estherbm/Open-BioBand/Images/3D/1.png

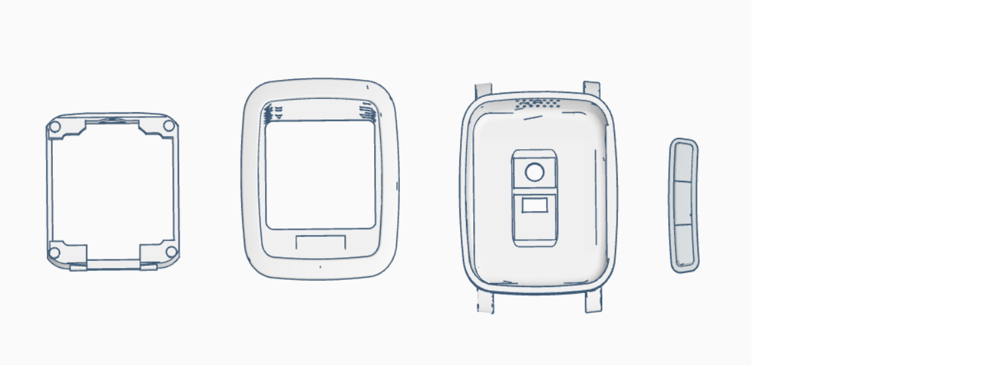
Images/3D/1.png
