estherbm/Open-BioBand/Images/3D/2.png

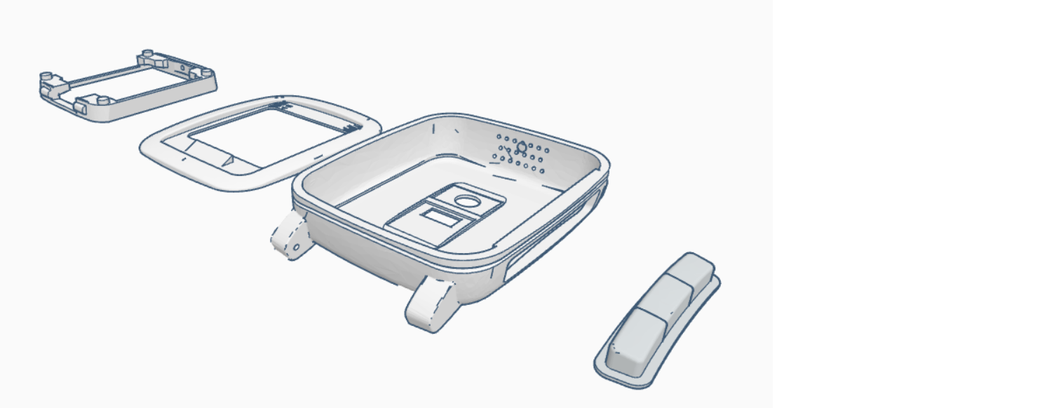
Images/3D/2.png
