estherbm/Open-BioBand/Images/3D/3.png

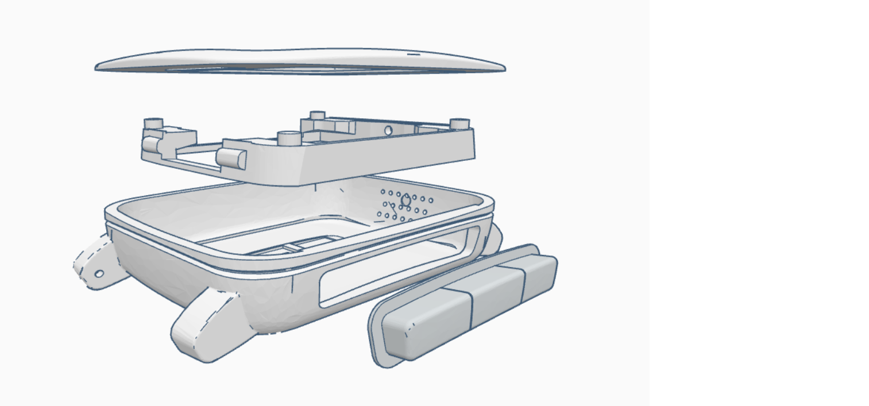
Images/3D/3.png
