estherbm/Open-BioBand/Images/3D/4.png

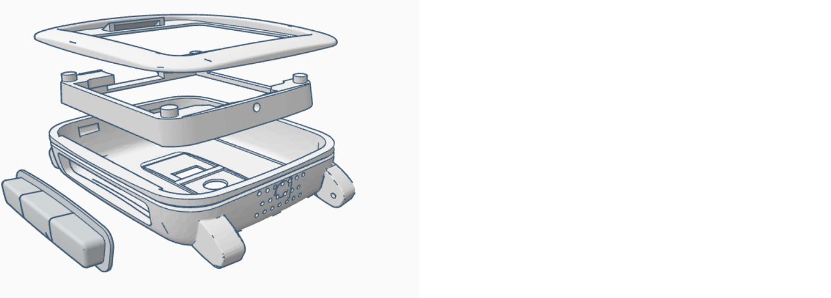
Images/3D/4.png
