estherbm/Open-BioBand/Images/3D/5.png

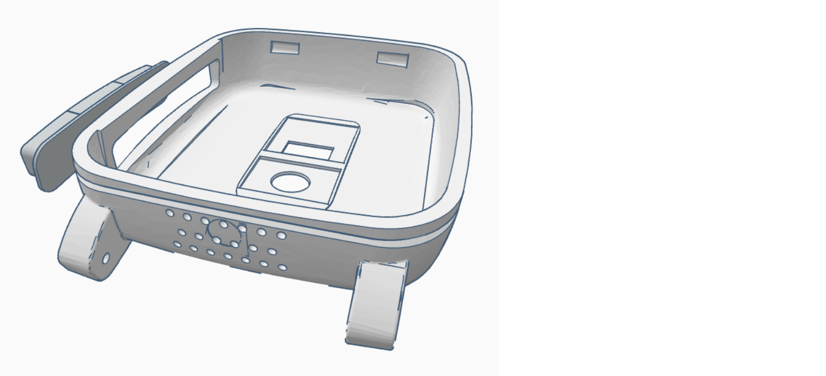
Images/3D/5.png
