estherbm/Open-BioBand/Images/3D/6.png

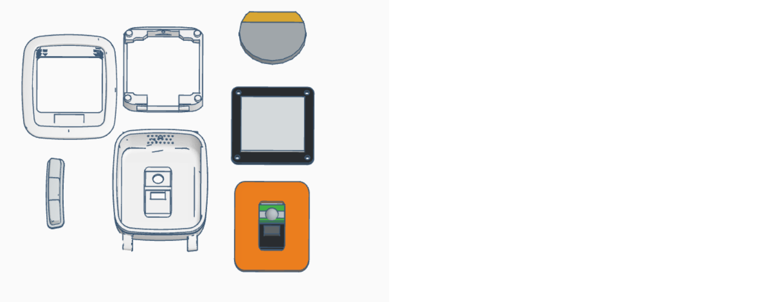
Images/3D/6.png
