estherbm/Open-BioBand/Images/3D/8.png

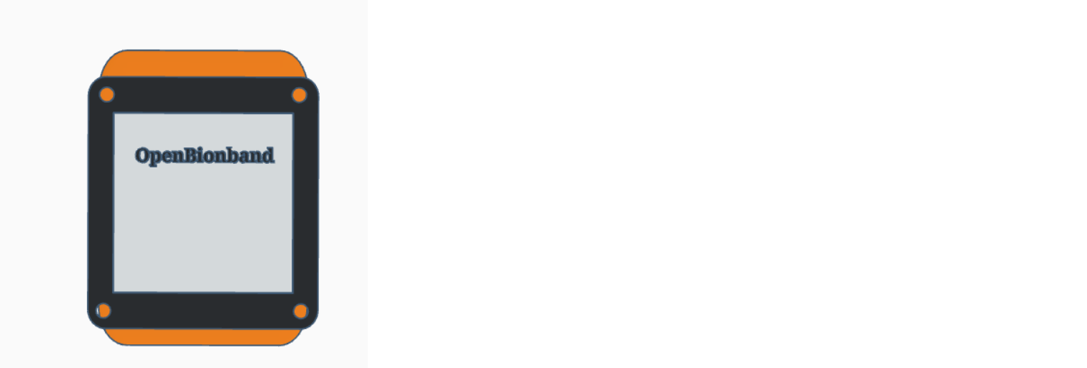
Images/3D/8.png
