estherbm/Open-BioBand/Images/3D/9.png

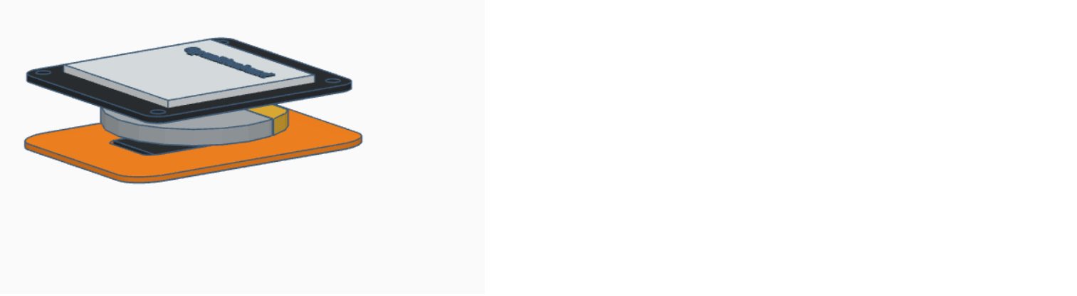
Images/3D/9.png
