estherbm/Open-BioBand/Images/3D/10.png

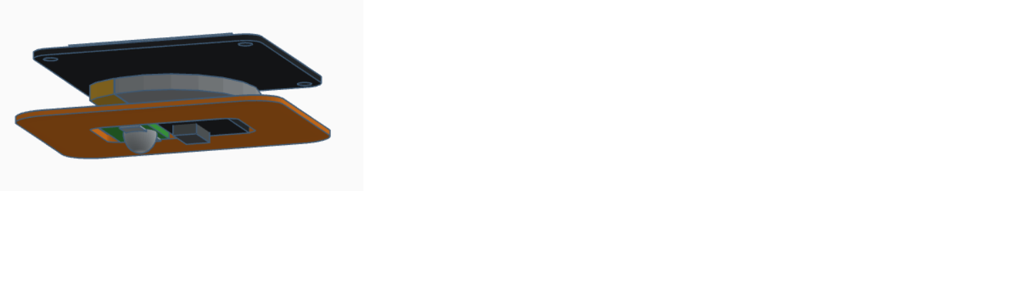
Images/3D/10.png
