estherbm/Open-BioBand/Images/3D/11.png

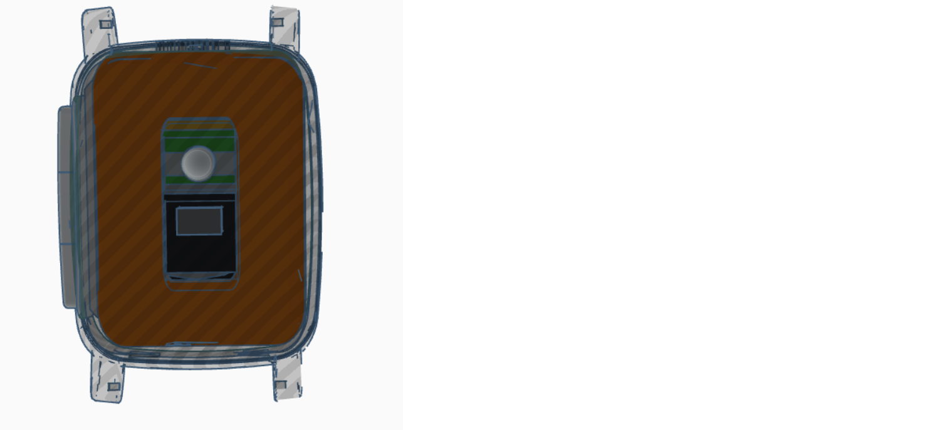
Images/3D/11.png
