estherbm/Open-BioBand/Images/3D/12.png

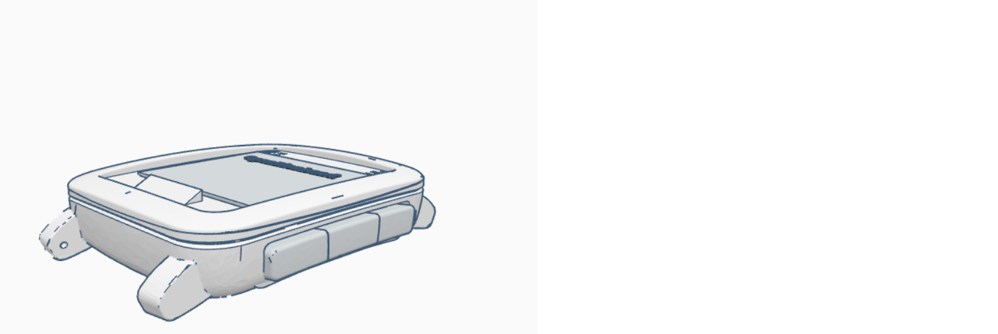
Images/3D/12.png
