estherbm/Open-BioBand/Images/3D/13.png

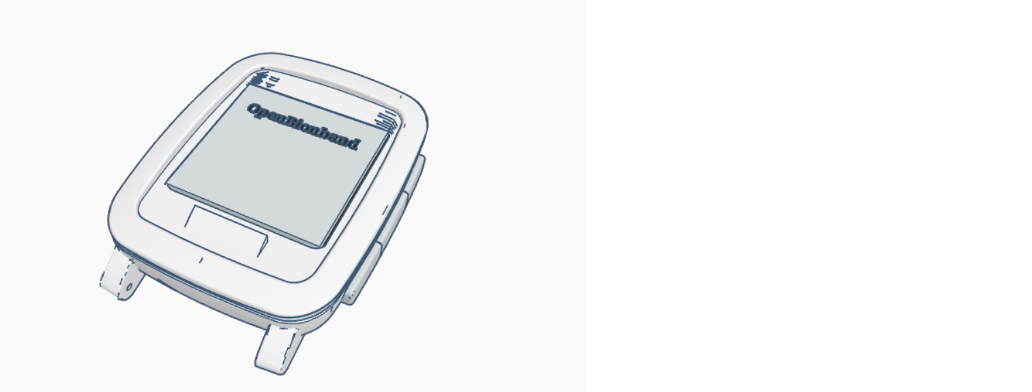
Images/3D/13.png
