estherbm/Open-BioBand/Images/3D/14.png

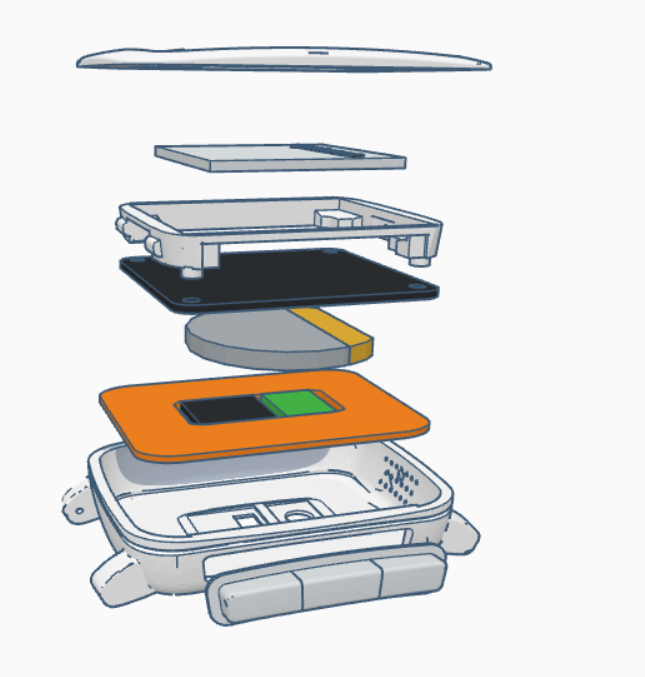
Images/3D/14.png
