estherbm/Open-BioBand/Images/3D/15.png

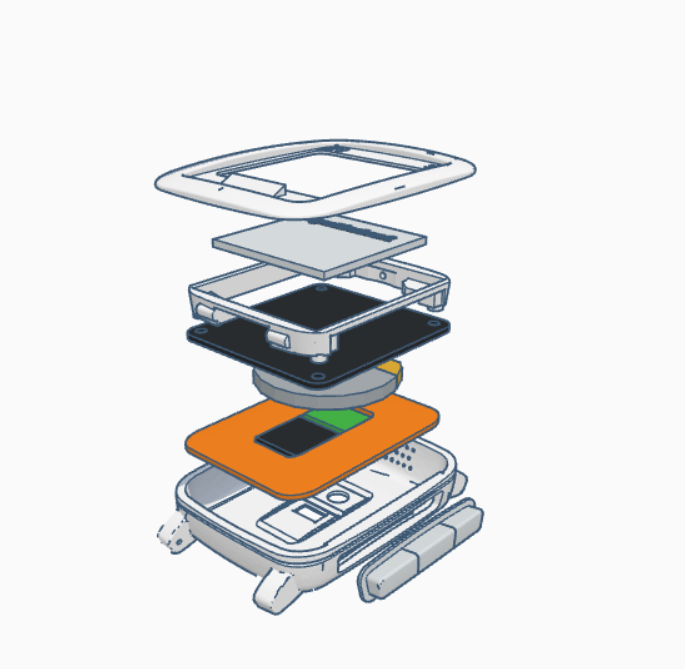
Images/3D/15.png
