estherbm/Open-BioBand/Images/3D/16.png

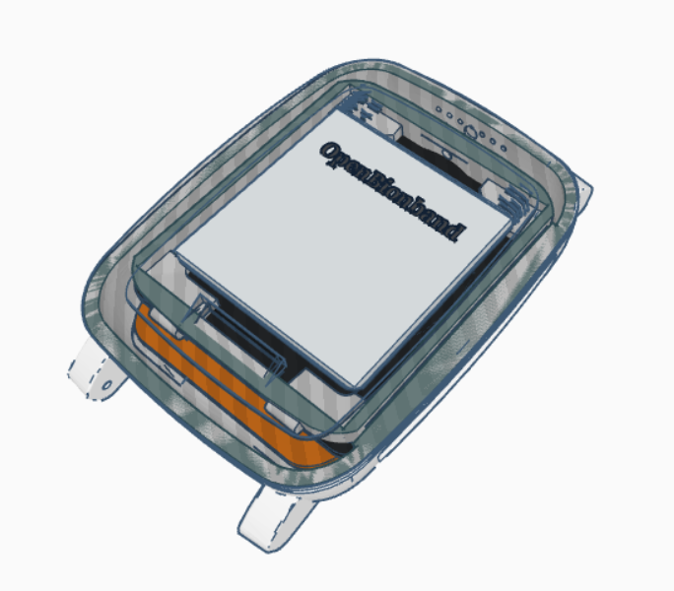
Images/3D/16.png
