estherbm/Open-BioBand/Images/Open_BioBand/1.jpg

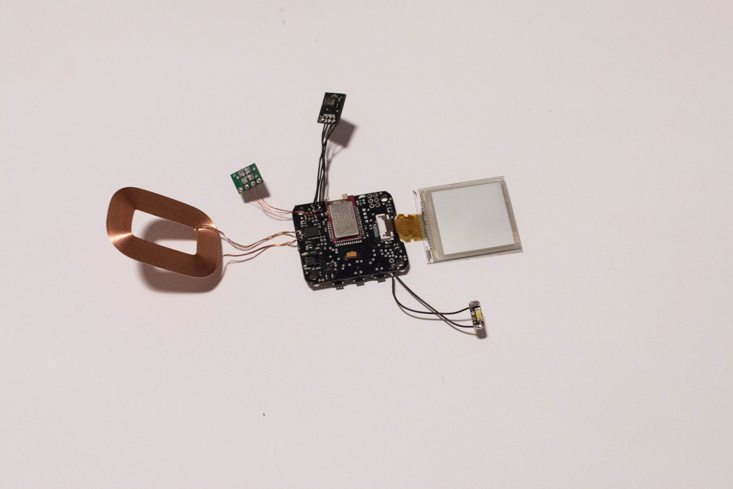
Images/Open_BioBand/1.jpg
