estherbm/Open-BioBand/Images/Open_BioBand/2.jpg

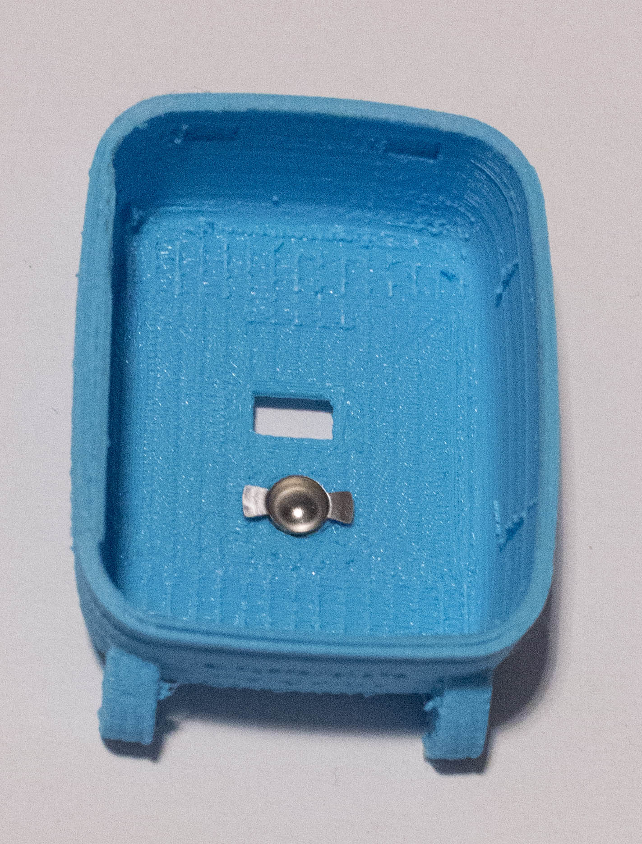
Images/Open_BioBand/2.jpg
