estherbm/Open-BioBand/Images/Open_BioBand/3.jpg

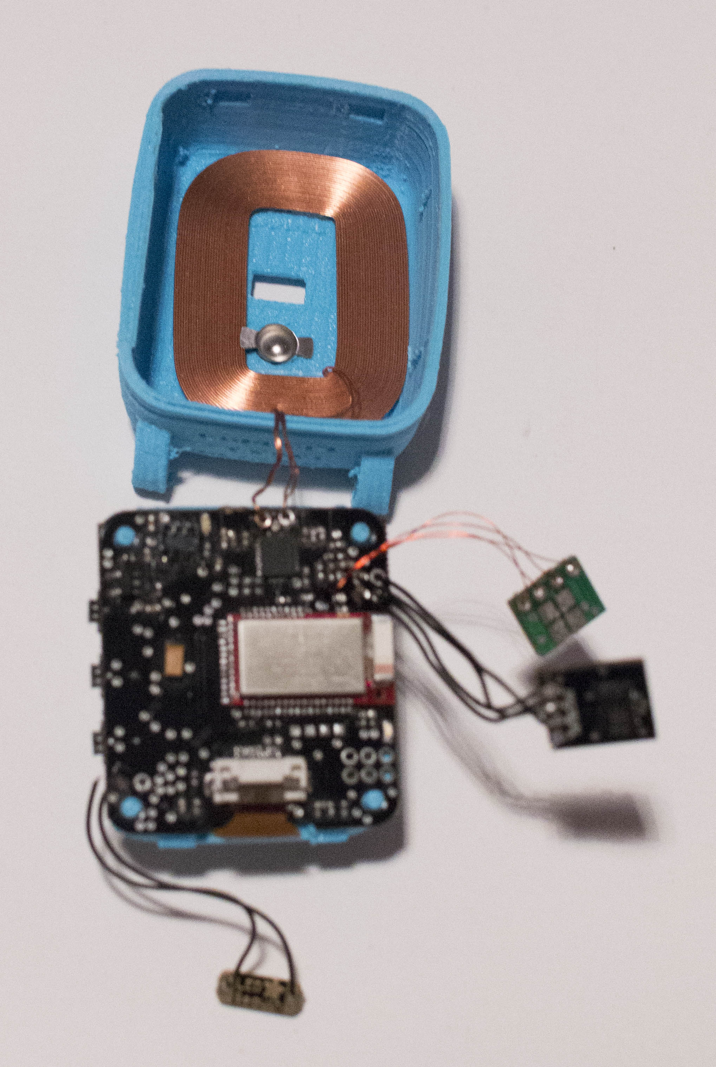
Images/Open_BioBand/3.jpg
