estherbm/Open-BioBand/Images/Open_BioBand/4.jpg

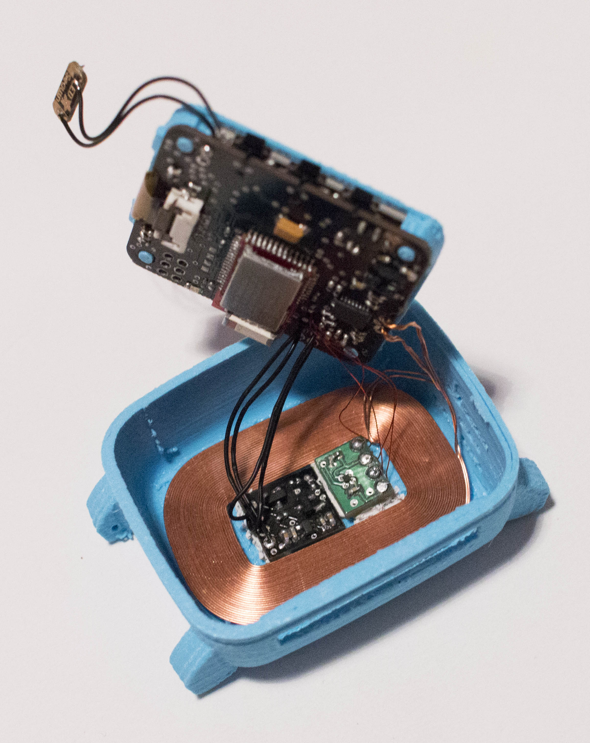
Images/Open_BioBand/4.jpg
