estherbm/Open-BioBand/Images/Open_BioBand/5.jpg

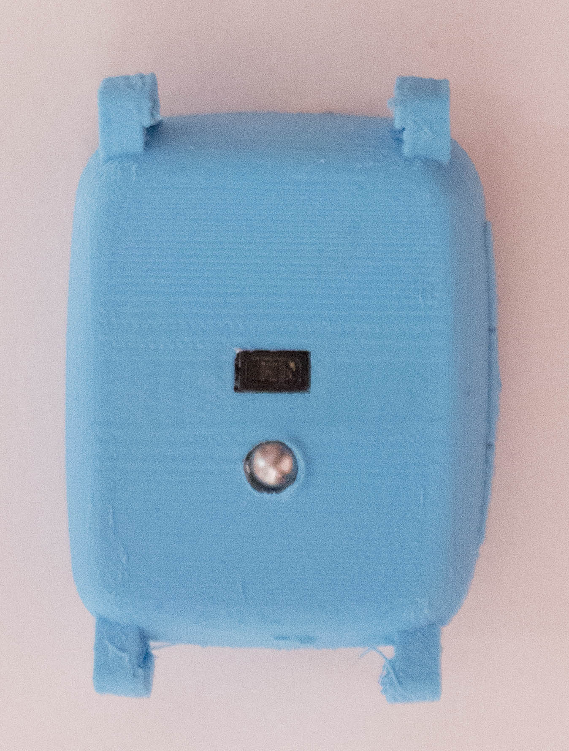
Images/Open_BioBand/5.jpg
