estherbm/Open-BioBand/Images/Open_BioBand/6.jpg

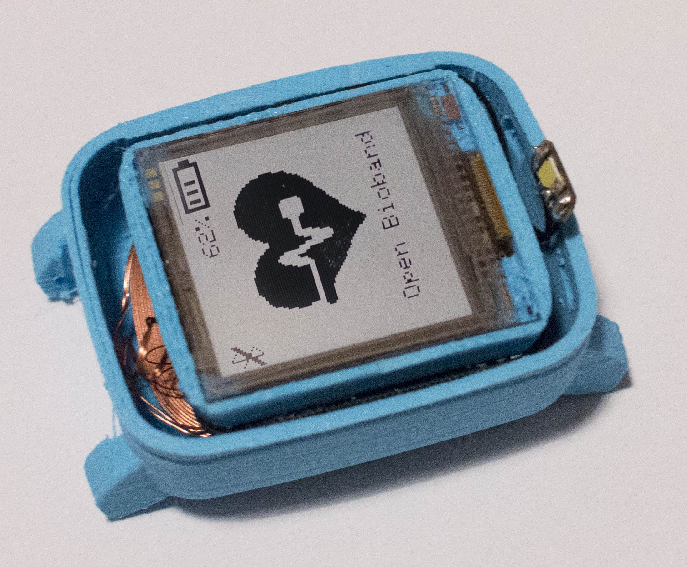
Images/Open_BioBand/6.jpg
