estherbm/Open-BioBand/Images/Open_BioBand/7.jpg

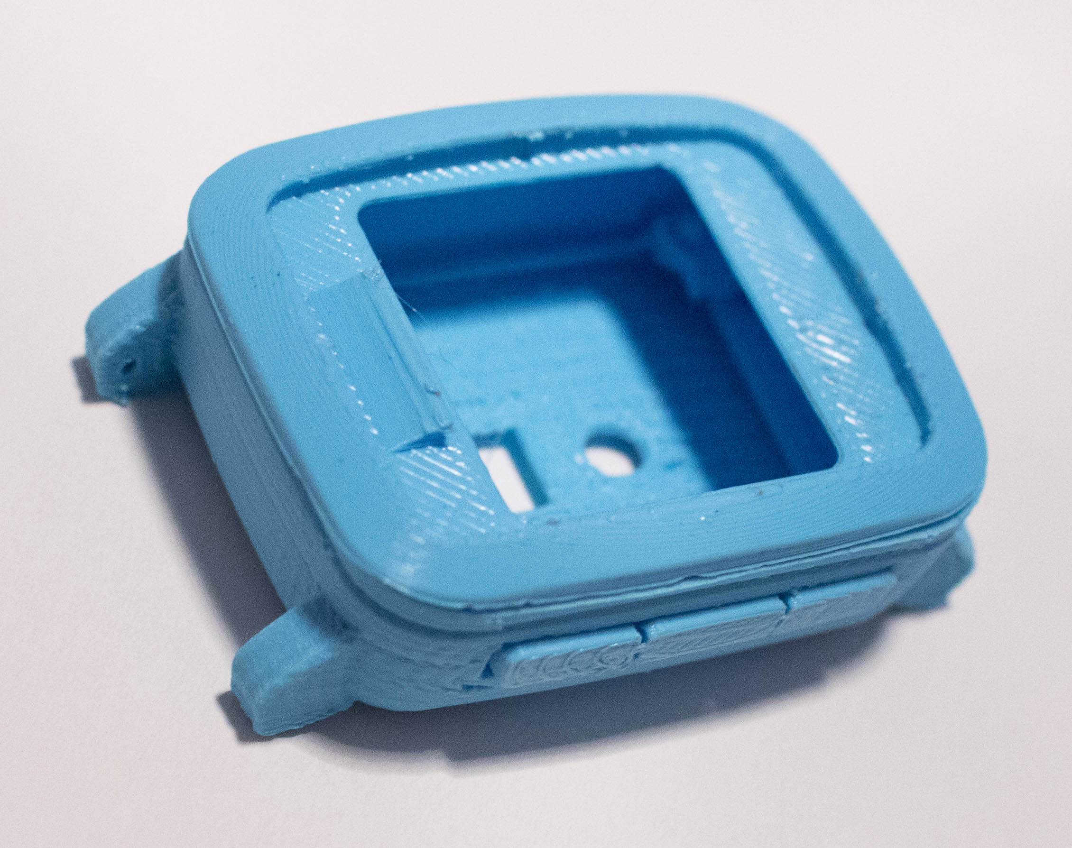
Images/Open_BioBand/7.jpg
