estherbm/Open-BioBand/Images/Open_BioBand/8.jpg

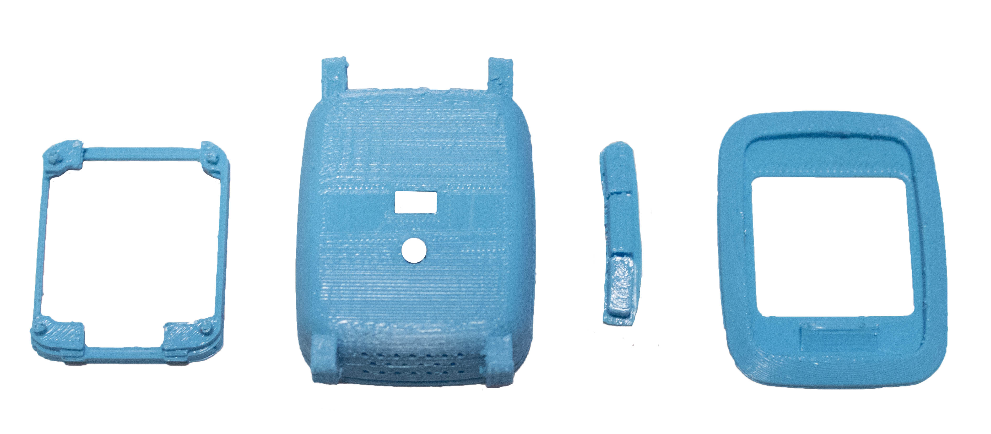
Images/Open_BioBand/8.jpg
