estherbm/Open-BioBand/Images/Open_BioBand/9.jpg

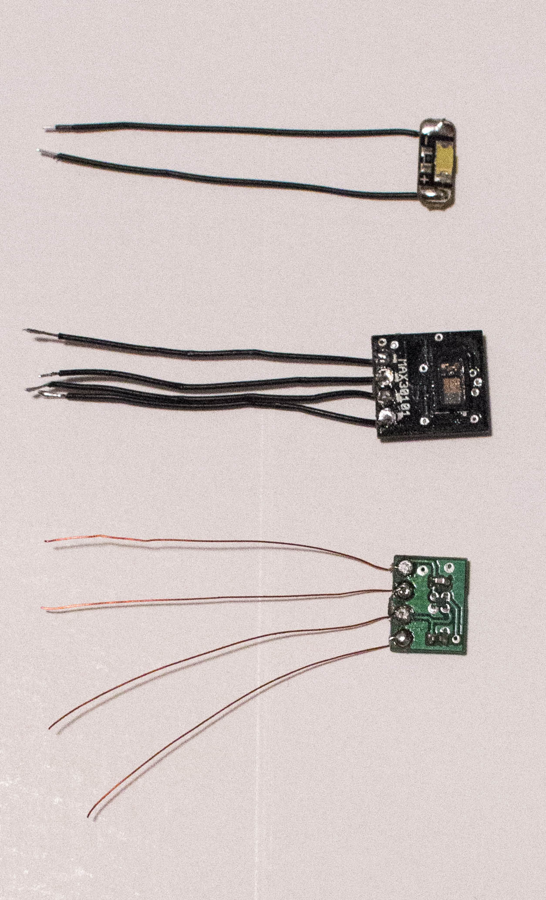
Images/Open_BioBand/9.jpg
