estherbm/Open-BioBand/Images/Open_BioBand/Final.jpg

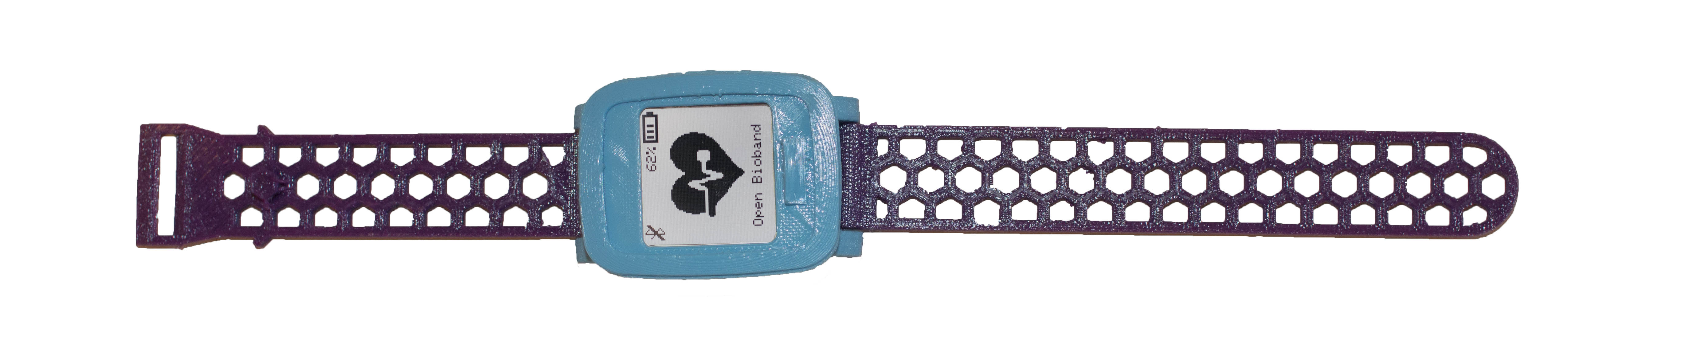
Images/Open_BioBand/Final.jpg
