estherbm/Open-BioBand/Images/PCBs/BioBand_v0-A.jpg

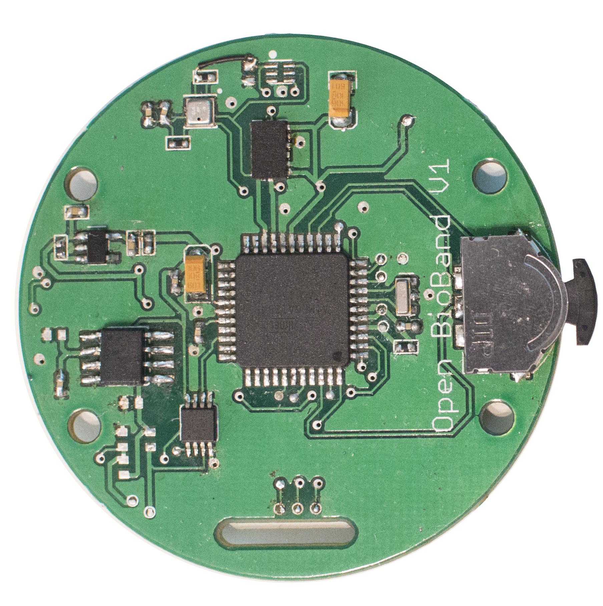
Images/PCBs/BioBand_v0-A.jpg
