estherbm/Open-BioBand/Images/PCBs/BioBand_v0-B.jpg

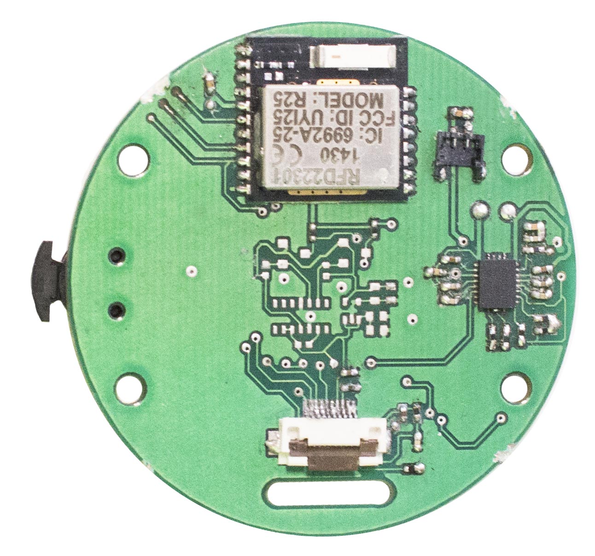
Images/PCBs/BioBand_v0-B.jpg
