estherbm/Open-BioBand/Images/PCBs/BioBand_v1-A.jpg

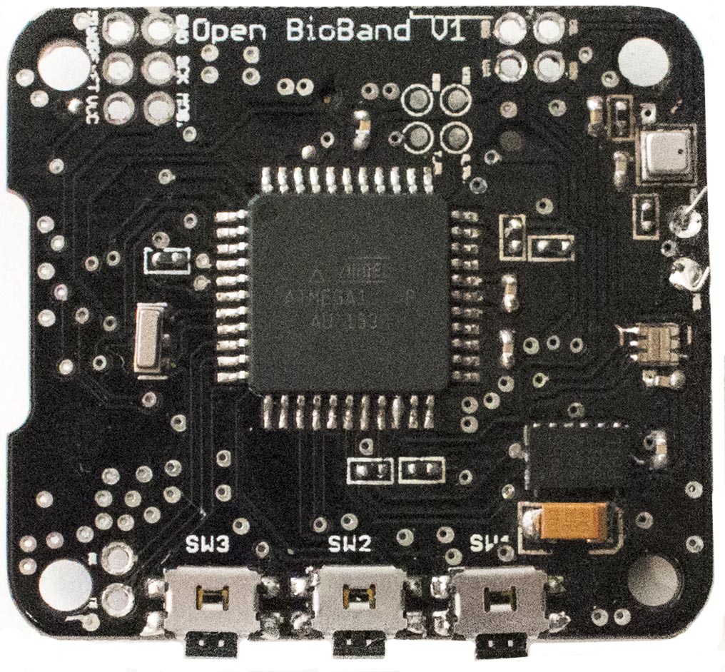
Images/PCBs/BioBand_v1-A.jpg
