estherbm/Open-BioBand/Images/PCBs/BioBand_v1-B.jpg

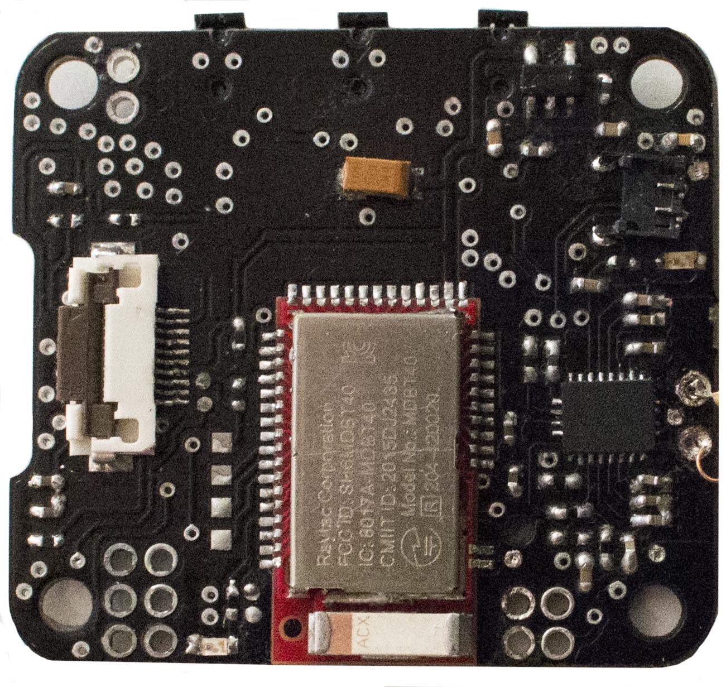
Images/PCBs/BioBand_v1-B.jpg
