estherbm/Open-BioBand/Images/PCBs/ICSP.jpg

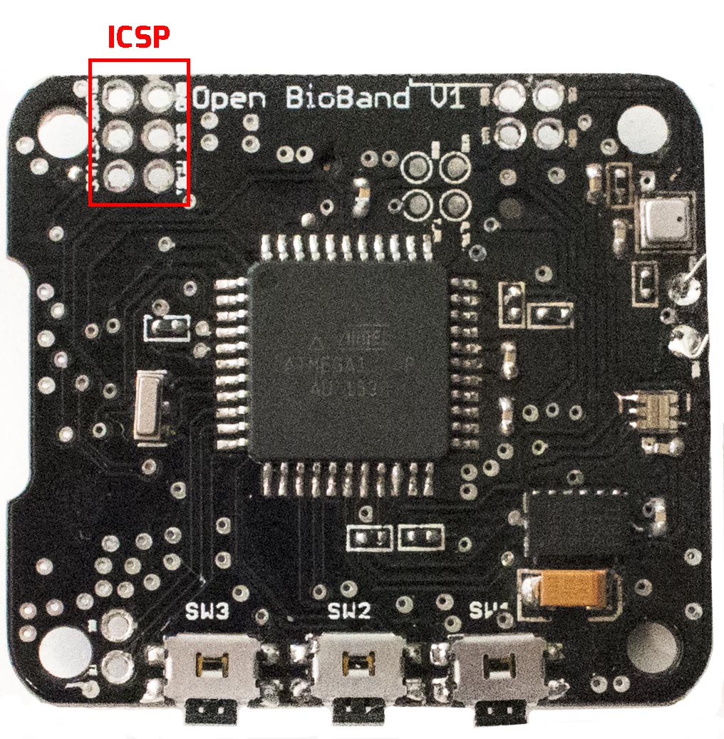
Images/PCBs/ICSP.jpg
