estherbm/Open-BioBand/Images/PCBs/LMT70-A.jpg

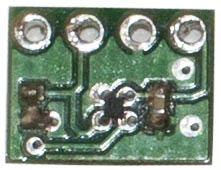
Images/PCBs/LMT70-A.jpg
