estherbm/Open-BioBand/Images/PCBs/LMT70-B.jpg

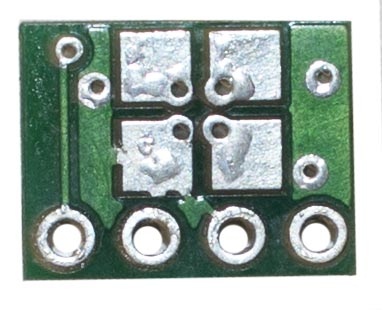
Images/PCBs/LMT70-B.jpg
