estherbm/Open-BioBand/Images/PCBs/M0-A.jpg

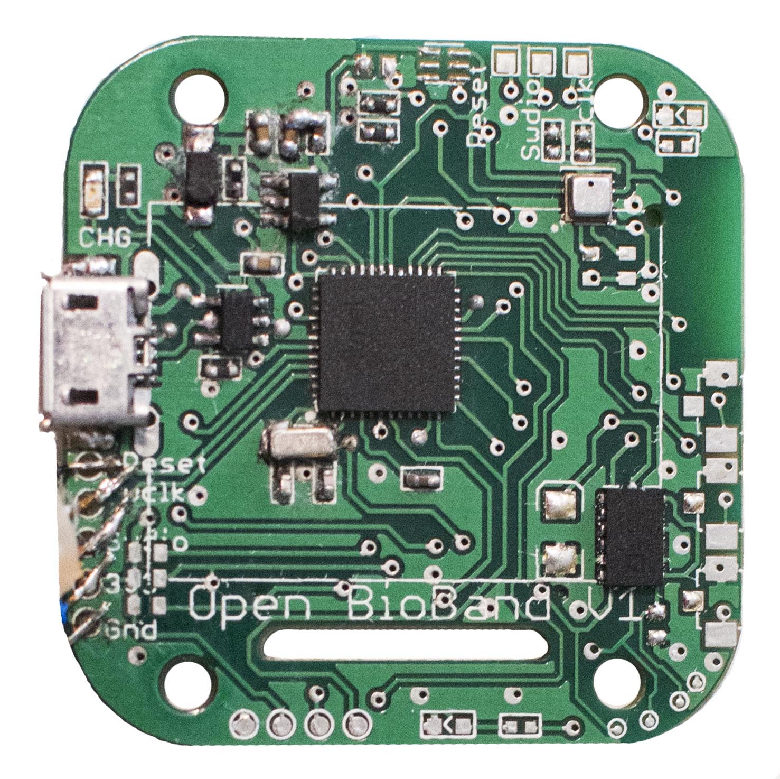
Images/PCBs/M0-A.jpg
