estherbm/Open-BioBand/Images/PCBs/MAX30101-A.jpg

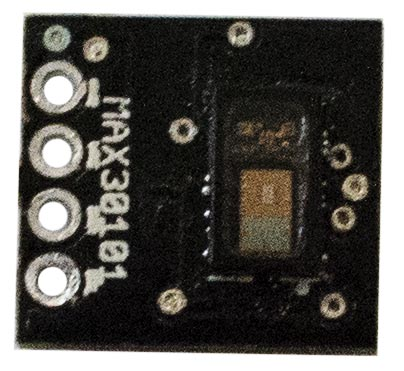
Images/PCBs/MAX30101-A.jpg
