estherbm/Open-BioBand/Images/PCBs/MAX30101_v0.jpg

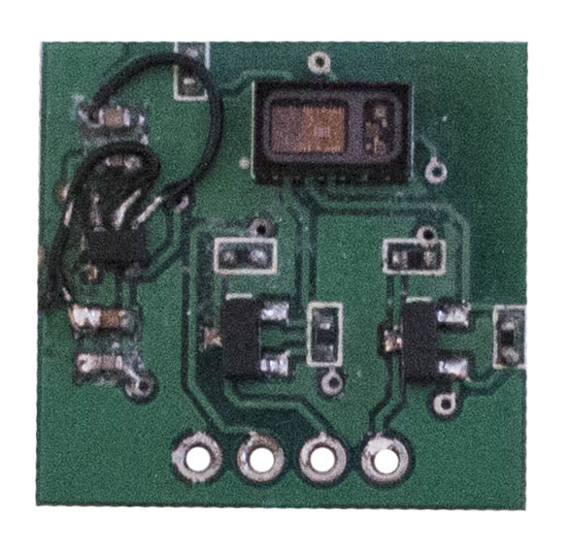
Images/PCBs/MAX30101_v0.jpg
