estherbm/Open-BioBand/Images/Screen/Clock.jpg

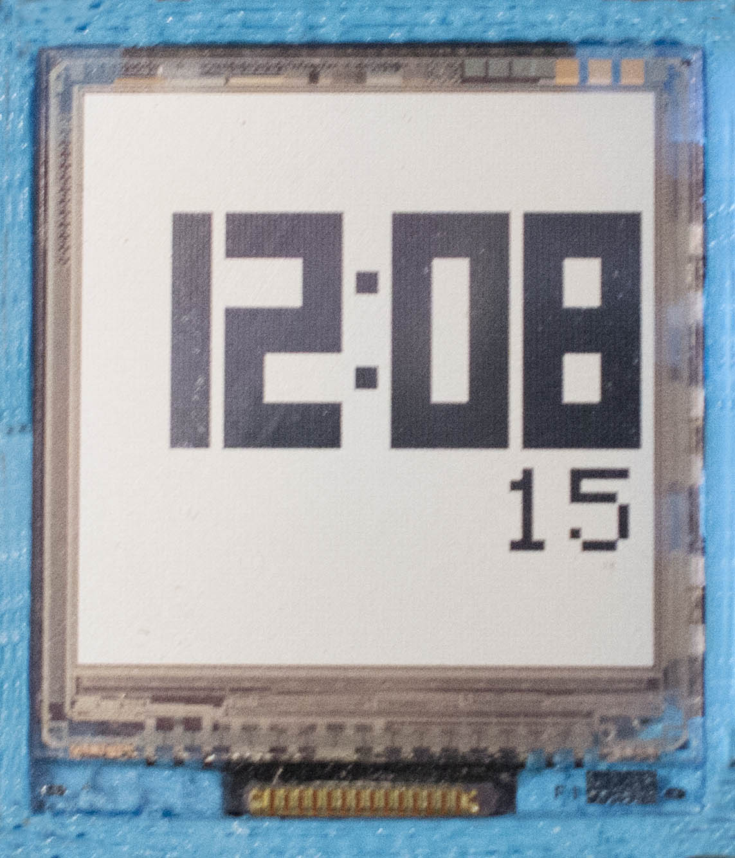
Images/Screen/Clock.jpg
