estherbm/Open-BioBand/Images/Screen/Configuration.jpg

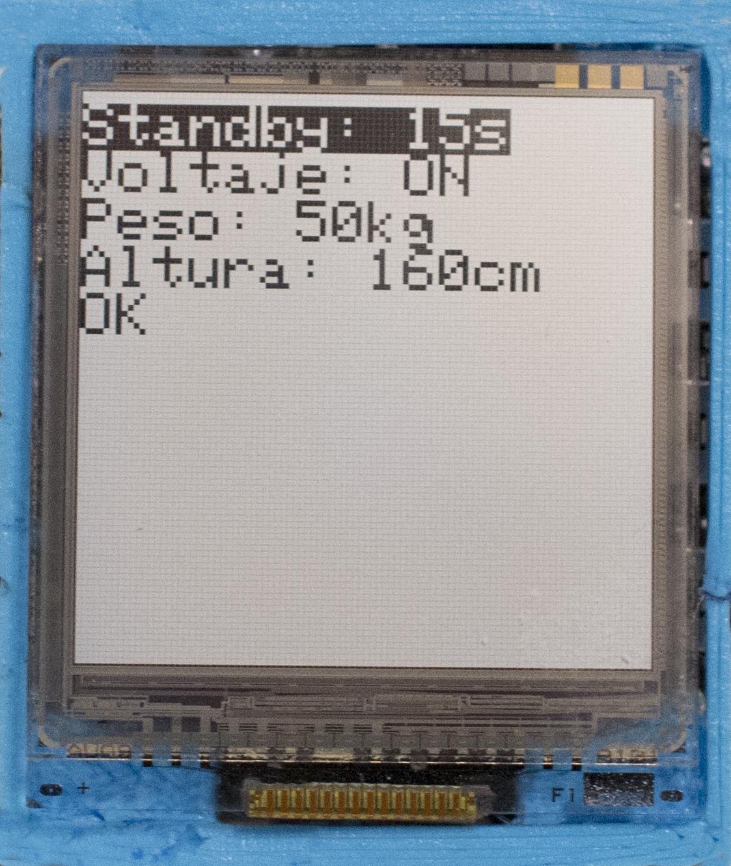
Images/Screen/Configuration.jpg
