estherbm/Open-BioBand/Images/Screen/Crono.jpg

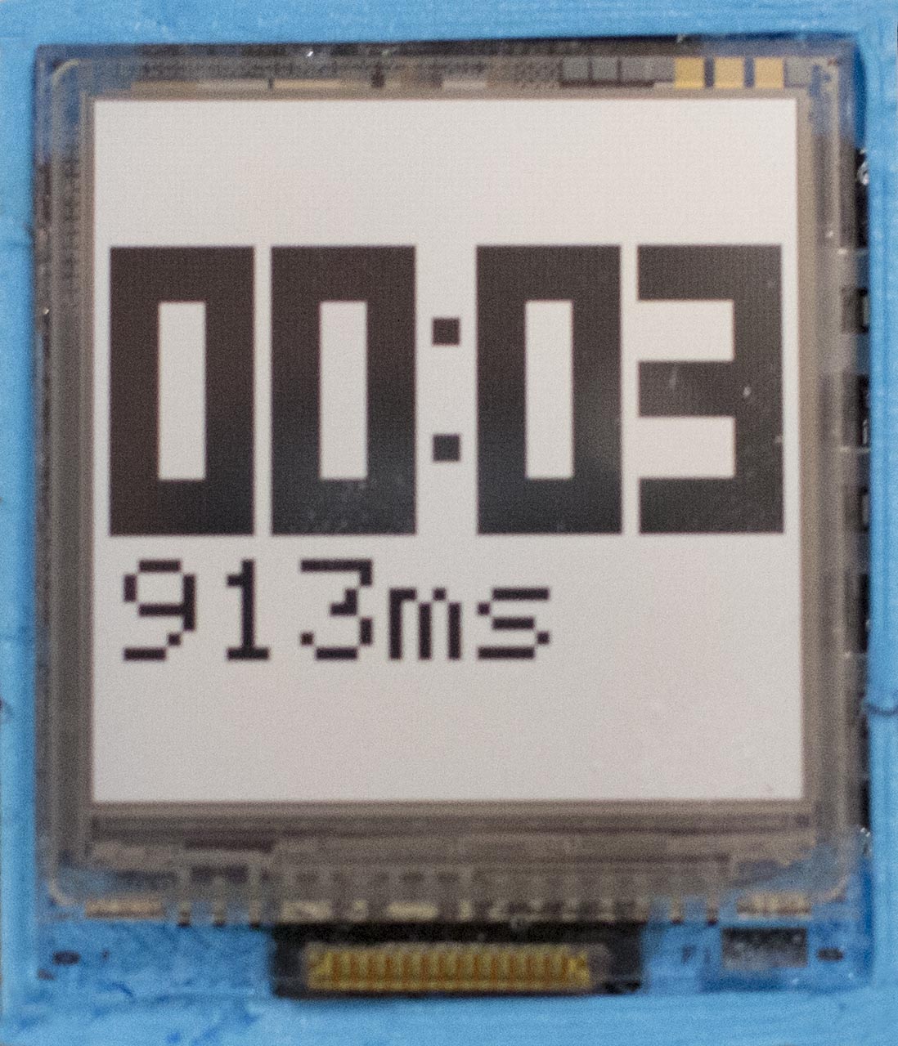
Images/Screen/Crono.jpg
