estherbm/Open-BioBand/Images/Screen/Environment.jpg

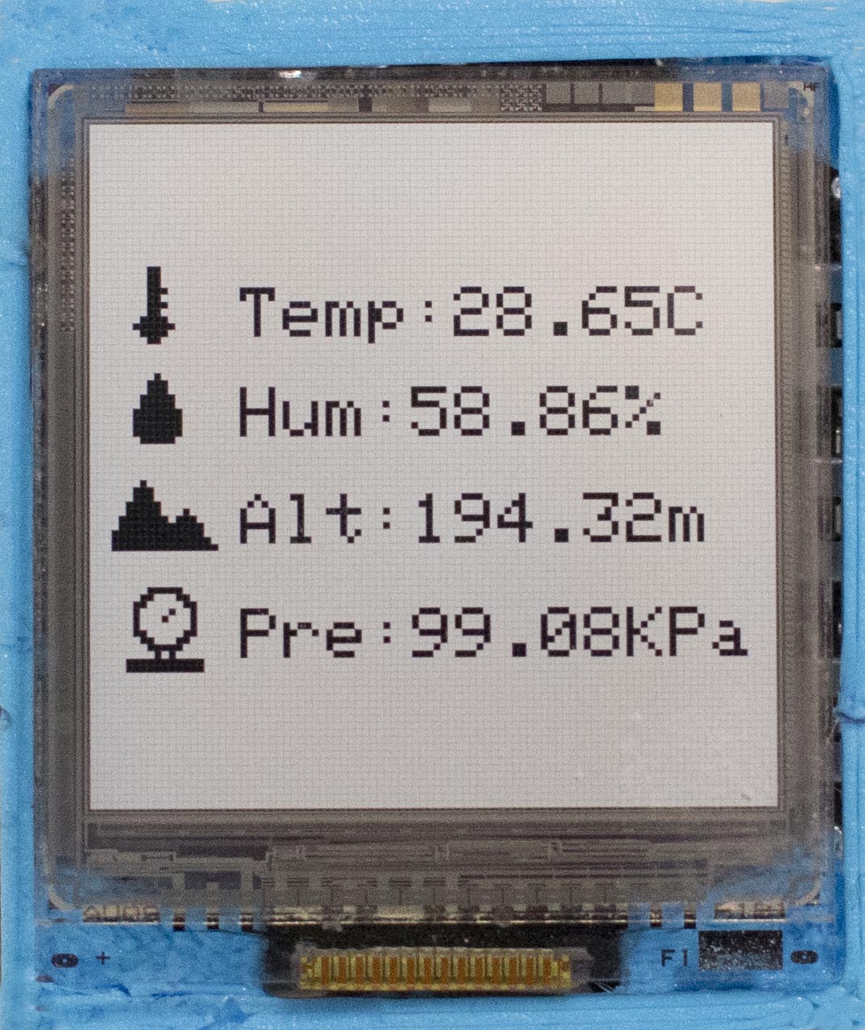
Images/Screen/Environment.jpg
