estherbm/Open-BioBand/Images/Screen/Game.png

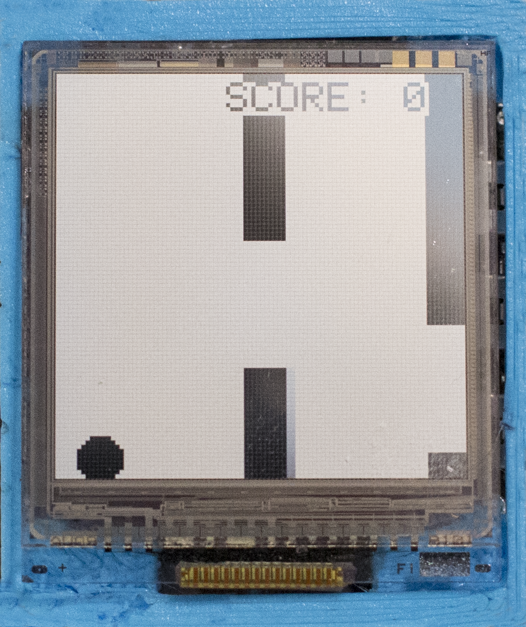
Images/Screen/Game.png
