estherbm/Open-BioBand/Images/Screen/GameOver.png

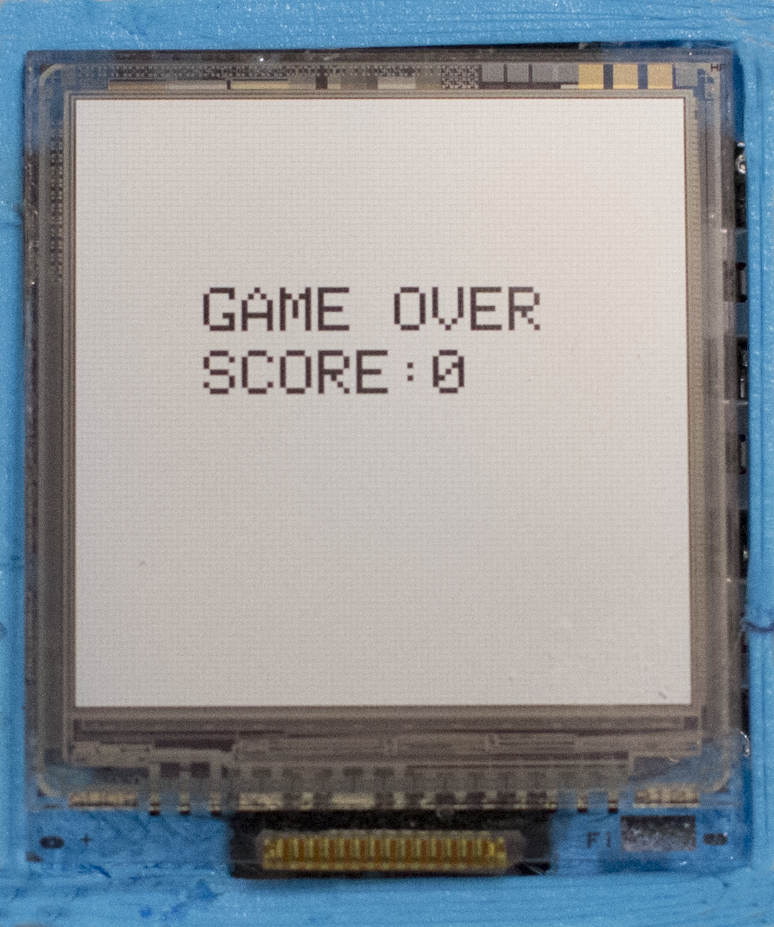
Images/Screen/GameOver.png
