estherbm/Open-BioBand/Images/Screen/Health.jpg

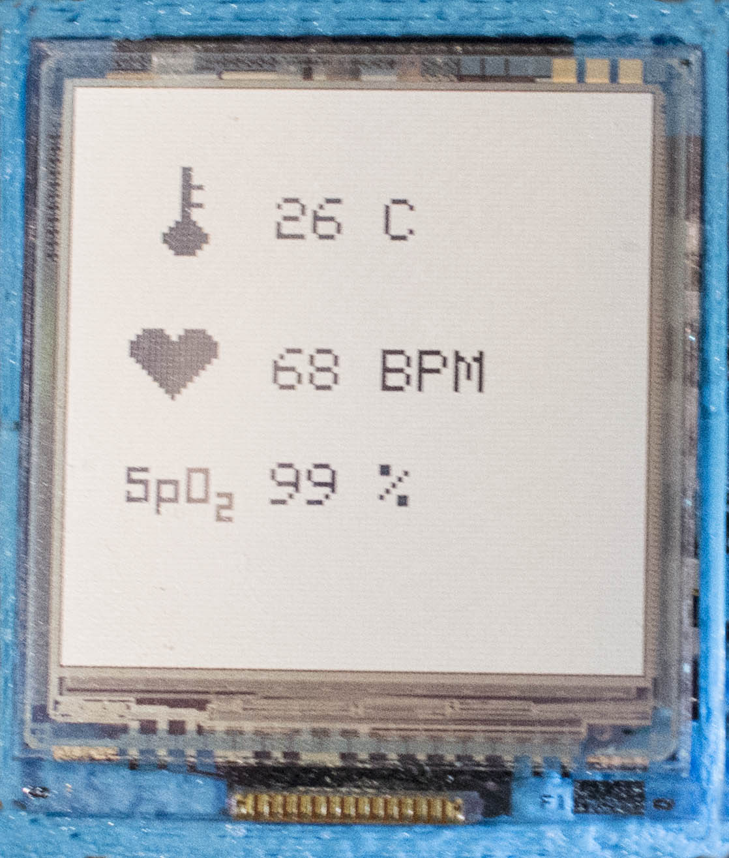
Images/Screen/Health.jpg
