estherbm/Open-BioBand/Images/Screen/Light.jpg

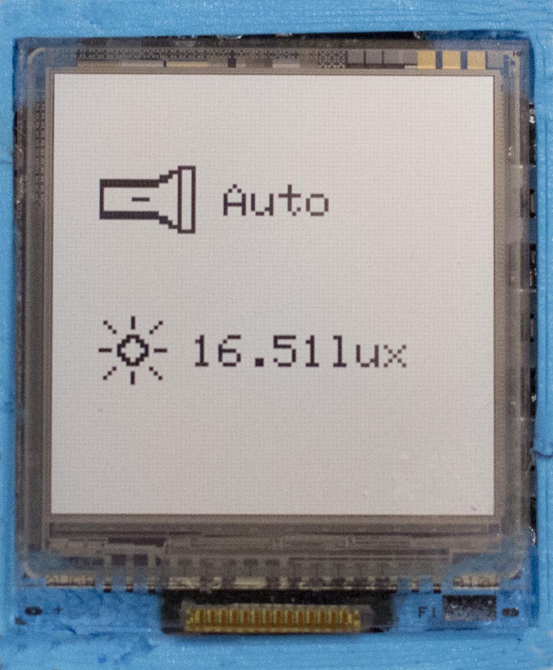
Images/Screen/Light.jpg
