estherbm/Open-BioBand/Images/Screen/Main.jpg

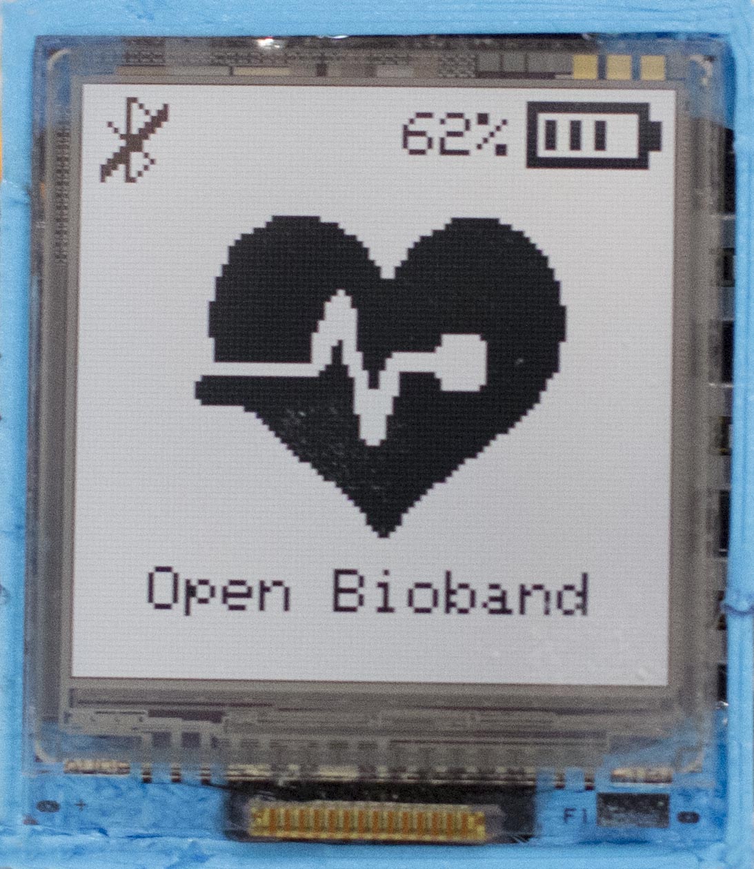
Images/Screen/Main.jpg
