estherbm/Open-BioBand/Images/Screen/Menu.jpg

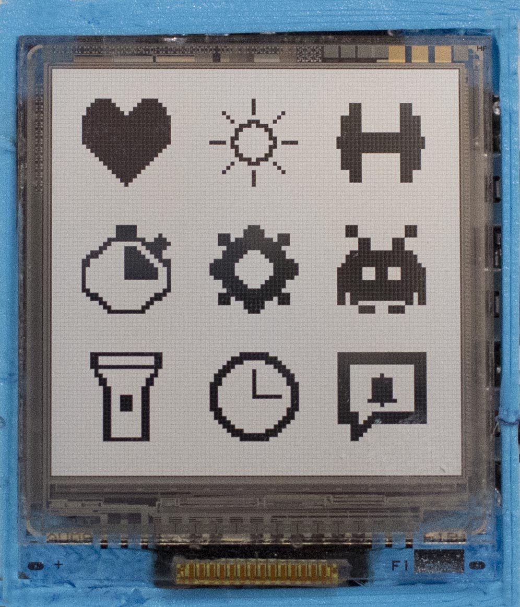
Images/Screen/Menu.jpg
