estherbm/Open-BioBand/Images/Screen/Motion.jpg

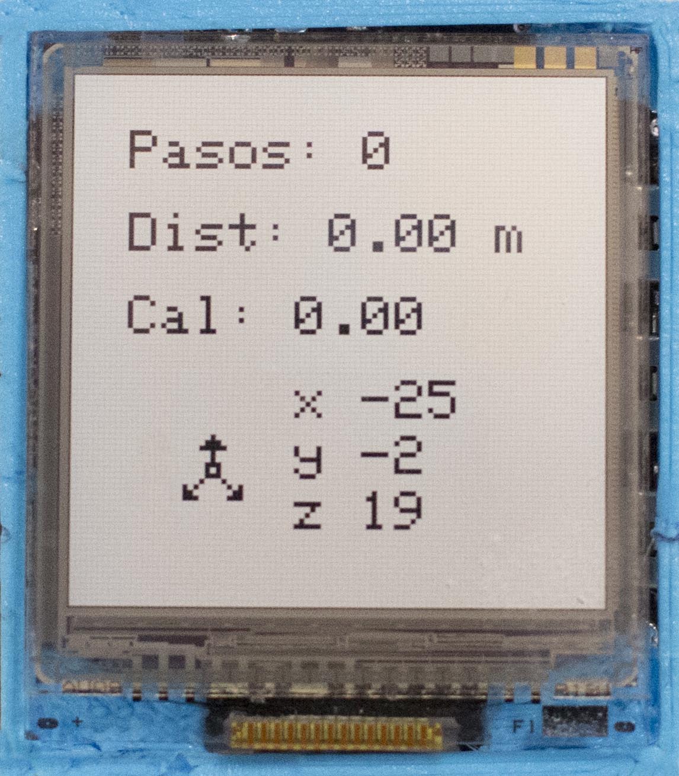
Images/Screen/Motion.jpg
