estherbm/Open-BioBand/Images/Screen/Notifications.jpg

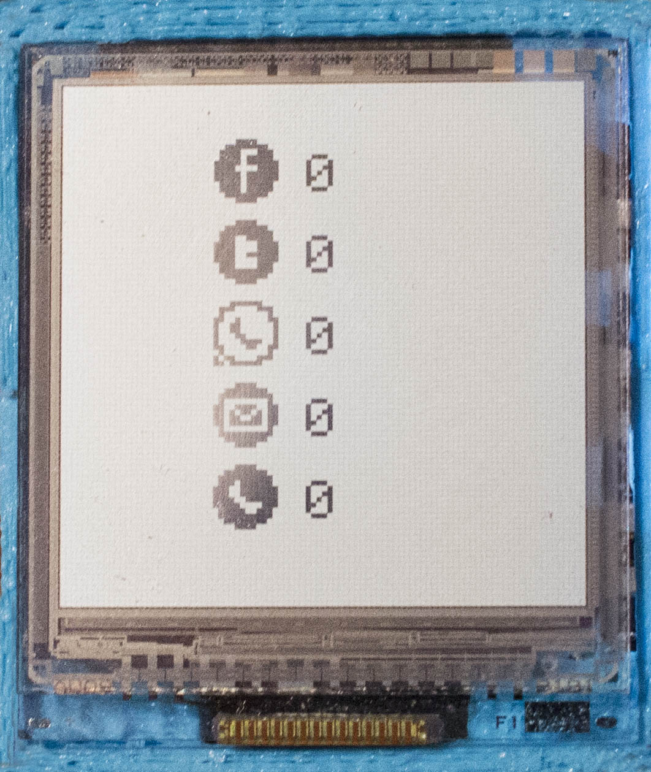
Images/Screen/Notifications.jpg
