estherbm/Open-BioBand/Images/Testing/1.jpg

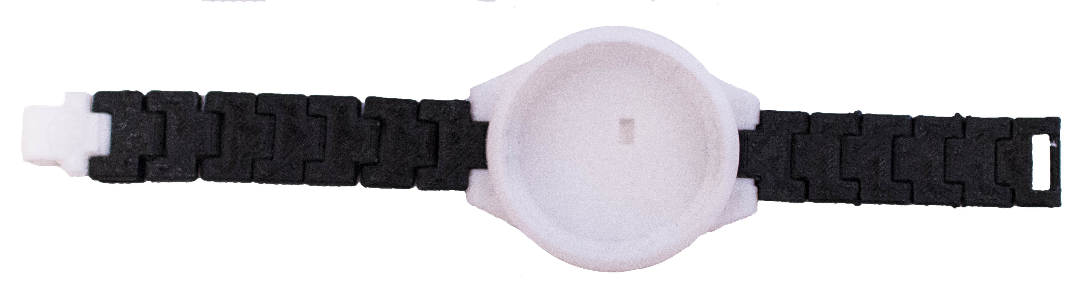
Images/Testing/1.jpg
