estherbm/Open-BioBand/Images/Testing/4.jpg

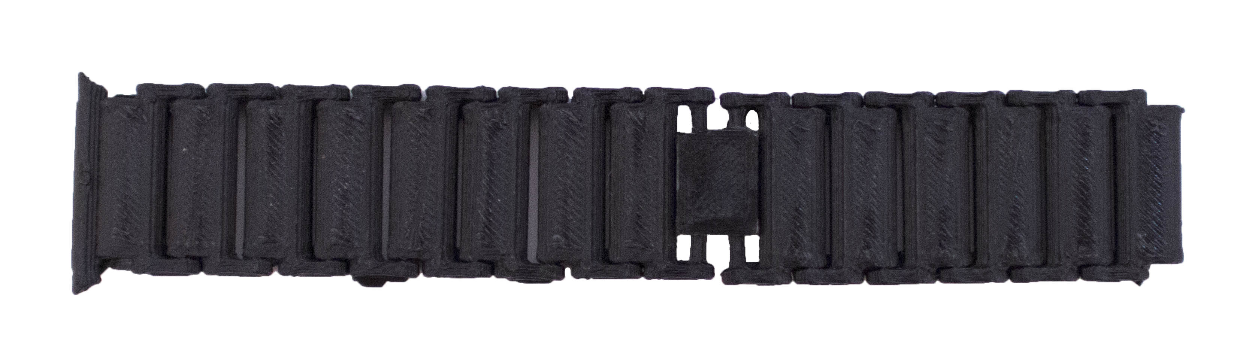
Images/Testing/4.jpg
