estherbm/Open-BioBand/Images/Testing/5.jpg

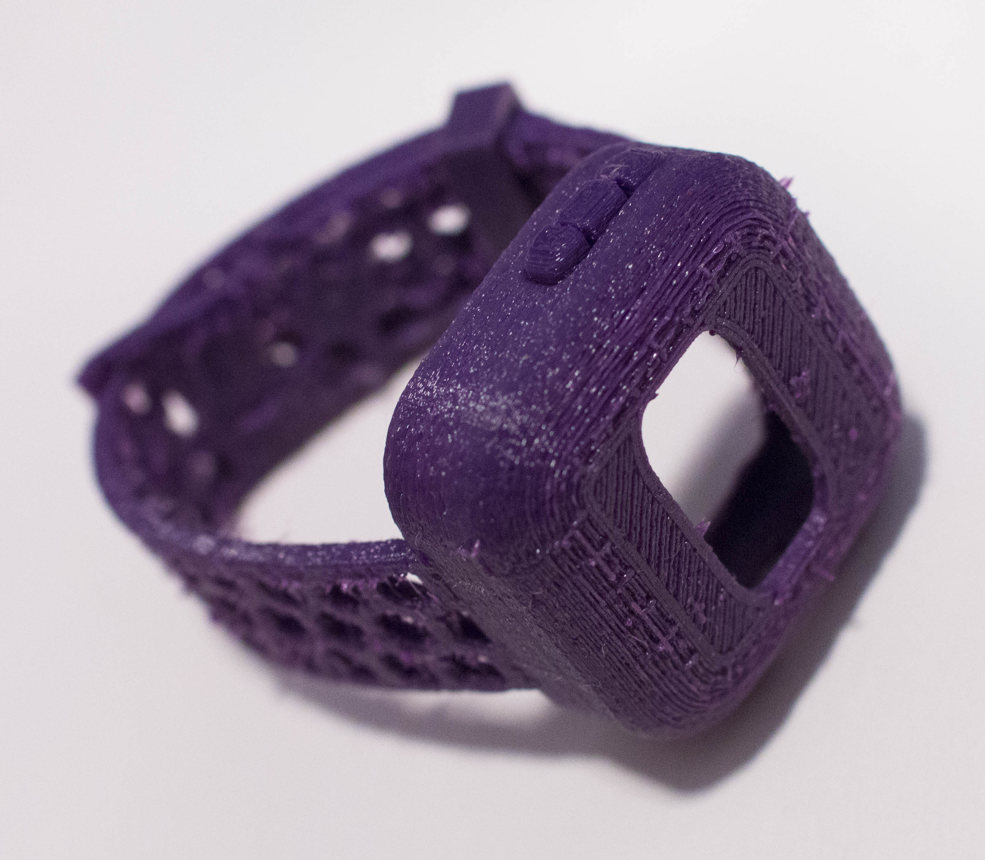
Images/Testing/5.jpg
