estherbm/Open-BioBand/Images/Testing/MAX30101-A_test.jpg

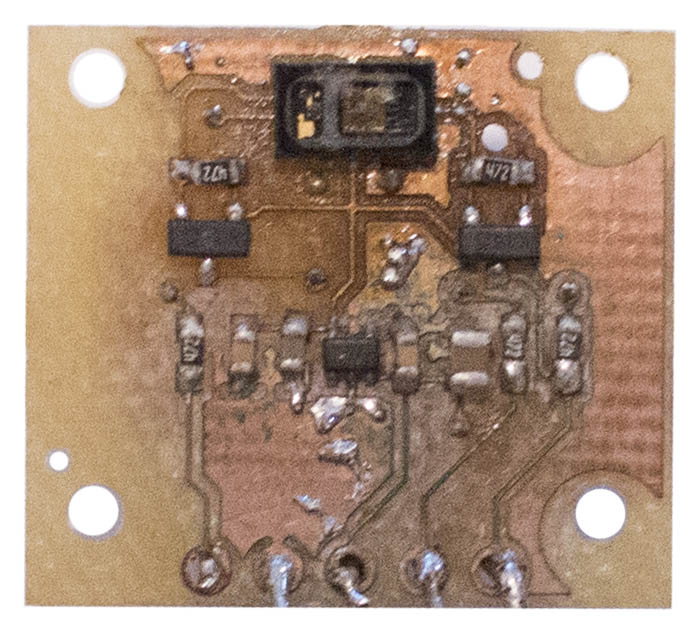
Images/Testing/MAX30101-A_test.jpg
