estherbm/Open-BioBand/Images/Testing/QiCharging1.jpg

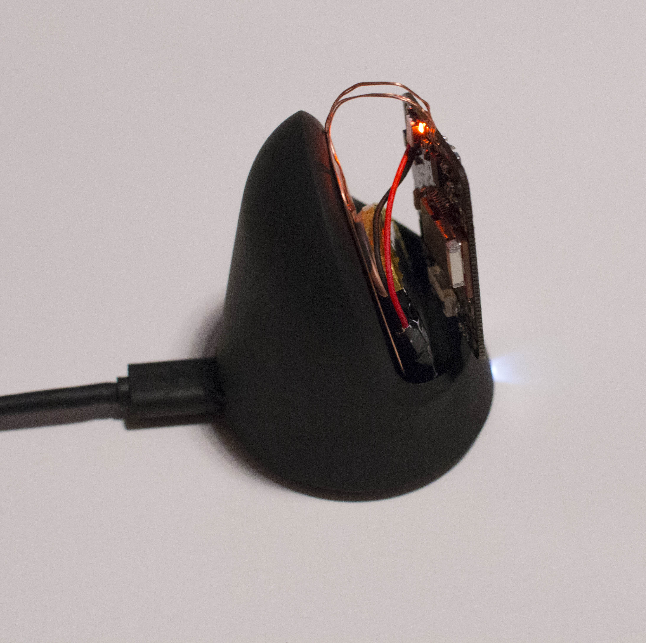
Images/Testing/QiCharging1.jpg
