estherbm/Open-BioBand/Code/Final/openbioband_v0.21/pantallaMenu.ino

/*******************************************************************************
   Pantalla Menú
 *******************************************************************************/

//!****************************************************************************
//!   Nombre: pantallaMenu
//!   Descripción: Pantalla menu principal para elegir pantalla de medición
//!   Parámetro entrada: void
//!   Parámetro salida: void
//!   Ejemplo: pantallaMenu();
//!****************************************************************************

void pantallaMenu() {

  // Definición logos
  #define anchoIcono 25
  #define altoIcono  25
  
  static const unsigned char juegos_img_1[] PROGMEM =
  {
    0x0, 0x0, 0x0, 0x0,
    0x0, 0x0, 0x0, 0x0,
    0xe, 0x0, 0x38, 0x0,
    0xe, 0x0, 0x38, 0x0,
    0xe, 0x0, 0x38, 0x0,
    0x1, 0xc1, 0xc0, 0x0,
    0x1, 0xc1, 0xc0, 0x0,
    0x1, 0xc1, 0xc0, 0x0,
    0x7, 0xff, 0xf0, 0x0,
    0xf, 0xff, 0xf8, 0x0,
    0xf, 0xff, 0xf8, 0x0,
    0x1f, 0xff, 0xfc, 0x0,
    0x3f, 0x1c, 0x7e, 0x0,
    0x3f, 0x1c, 0x7e, 0x0,
    0x3f, 0x1c, 0x7e, 0x0,
    0x3f, 0xff, 0xfe, 0x0,
    0x3f, 0xff, 0xfe, 0x0,
    0x3f, 0xff, 0xfe, 0x0,
    0x37, 0xff, 0xf6, 0x0,
    0x37, 0xff, 0xf6, 0x0,
    0x36, 0x0, 0x36, 0x0,
    0x1, 0xe3, 0xc0, 0x0,
    0x1, 0xe3, 0xc0, 0x0,
    0x0, 0x0, 0x0, 0x0,
    0x0, 0x0, 0x0, 0x0
  };

  static const unsigned char juegos_img_2[] PROGMEM =
  {
    0xff, 0xff, 0xff, 0x80,
    0xff, 0xff, 0xff, 0x80,
    0xf1, 0xff, 0xc7, 0x80,
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

  // Visualización menu principal
  display.setTextSize(1);
  display.setTextColor(NEGRO, BLANCO);

  if (menuVal != 1) {
    display.drawBitmap(5, 5, salud_img_1, anchoIcono, altoIcono, NEGRO);
  } else {
    display.drawBitmap(5, 5, salud_img_2, anchoIcono, altoIcono, NEGRO);
  }

  if (menuVal != 2) {
    display.drawBitmap(35, 5, tiempo_img_1, anchoIcono, altoIcono, NEGRO);
  } else {
    display.drawBitmap(35, 5, tiempo_img_2, anchoIcono, altoIcono, NEGRO);
  }

  if (menuVal != 3) {
    display.drawBitmap(65, 5, pasos_img_1, anchoIcono, altoIcono, NEGRO);
  } else {
    display.drawBitmap(65, 5, pasos_img_2, anchoIcono, altoIcono, NEGRO);
  }

  if (menuVal != 4) {
    display.drawBitmap(5, 35, crono_img_1, anchoIcono, altoIcono, NEGRO);
  } else {
    display.drawBitmap(5, 35, crono_img_2, anchoIcono, altoIcono, NEGRO);
  }

  if (menuVal != 5) {
    display.drawBitmap(35, 35, conf_img_1, anchoIcono, altoIcono, NEGRO);
  } else {
    display.drawBitmap(35, 35, conf_img_2, anchoIcono, altoIcono, NEGRO);
  }

  if (menuVal != 6) {
    display.drawBitmap(65, 35, juegos_img_1, anchoIcono, altoIcono, NEGRO);
  } else {
    display.drawBitmap(65, 35, juegos_img_2, anchoIcono, altoIcono, NEGRO);
  }
  if (menuVal != 7) {
    display.drawBitmap(5, 65, ILUMINACION_img_1, anchoIcono, altoIcono, NEGRO);
  } else {
    display.drawBitmap(5, 65, ILUMINACION_img_2, anchoIcono, altoIcono, NEGRO);
  }

  if (menuVal != 8) {
    display.drawBitmap(35, 65, reloj_img_1, anchoIcono, altoIcono, NEGRO);
  } else {
    display.drawBitmap(35, 65, reloj_img_2, anchoIcono, altoIcono, NEGRO);
  }

  if (menuVal != 9) {
    display.drawBitmap(65, 65, notif_img_1, anchoIcono, altoIcono, NEGRO);
  } else {
    display.drawBitmap(65, 65, notif_img_2, anchoIcono, altoIcono, NEGRO);
  }
}

/*******************************************************************************/
