estherbm/Open-BioBand/Code/Others/prueba_ambiente/prueba_ambiente.ino

#include <SPI.h>
#include <SD.h>
#include <math.h>
#include <ADXL362.h>
#include <OneWire.h> 
#include <SHT1X.h>
#include <stdint.h>
#include "SparkFunBME280.h"
//Library allows either I2C or SPI, so include both.
#include "Wire.h"
#include "SPI.h"

//SHT15
//variables for storing values
float tempC = 0;
float tempF = 0;
float humidity = 0;

//Create an instance of the SHT1X sensor
SHT1x sht15(A4, A5);//Data, SCK
/////////////

//BME280
//Global sensor object
BME280 mySensor;
///////////////

//ADXL362 xl;
//int16_t temp;
//int16_t XValue, YValue, ZValue, Temperature;

int x=0;
const int chipSelect = 4;

//DS18B20
int DS18S20_Pin = 2; //DS18S20 Signal pin on digital 2

//Temperature chip i/o
OneWire ds(DS18S20_Pin);  // on digital pin 2
///////////

//NTC
double Thermistor(int RawADC) {
 double Temp;
 Temp = log(10000.0*((1024.0/RawADC-1))); 
 Temp = 1 / (0.001129148 + (0.000234125 + (0.0000000876741 * Temp * Temp ))* Temp );
 Temp = Temp - 273.15;          
 //Temp = (Temp * 9.0)/ 5.0 + 32.0; 
 return Temp;
}
////////////////

void setup() {
  // Open serial communications and wait for port to open:
  Serial.begin(9600);

  ////BME280
    //For I2C, enable the following and disable the SPI section
  mySensor.settings.commInterface = I2C_MODE;
  mySensor.settings.I2CAddress = 0x77;
    //renMode can be:
  //  0, Sleep mode
  //  1 or 2, Forced mode
  //  3, Normal mode
  mySensor.settings.runMode = 3; //Normal mode
  //tStandby can be:
  //  0, 0.5ms
  //  1, 62.5ms
  //  2, 125ms
  //  3, 250ms
  //  4, 500ms
  //  5, 1000ms
  //  6, 10ms
  //  7, 20ms
  mySensor.settings.tStandby = 0;
  
  //filter can be off or number of FIR coefficients to use:
  //  0, filter off
  //  1, coefficients = 2
  //  2, coefficients = 4
  //  3, coefficients = 8
  //  4, coefficients = 16
  mySensor.settings.filter = 0;
  
  //tempOverSample can be:
  //  0, skipped
  //  1 through 5, oversampling *1, *2, *4, *8, *16 respectively
  mySensor.settings.tempOverSample = 1;

  //pressOverSample can be:
  //  0, skipped
  //  1 through 5, oversampling *1, *2, *4, *8, *16 respectively
    mySensor.settings.pressOverSample = 1;
  
  //humidOverSample can be:
  //  0, skipped
  //  1 through 5, oversampling *1, *2, *4, *8, *16 respectively
  mySensor.settings.humidOverSample = 1;
  //Calling .begin() causes the settings to be loaded
  delay(10);  //Make sure sensor had enough time to turn on. BME280 requires 2ms to start up.
  Serial.println(mySensor.begin(), HEX);
  Serial.print("Displaying ID, reset and ctrl regs\n");
  
  Serial.print("ID(0xD0): 0x");
  Serial.println(mySensor.readRegister(BME280_CHIP_ID_REG), HEX);
  Serial.print("Reset register(0xE0): 0x");
  Serial.println(mySensor.readRegister(BME280_RST_REG), HEX);
  Serial.print("ctrl_meas(0xF4): 0x");
  Serial.println(mySensor.readRegister(BME280_CTRL_MEAS_REG), HEX);
  Serial.print("ctrl_hum(0xF2): 0x");
  Serial.println(mySensor.readRegister(BME280_CTRL_HUMIDITY_REG), HEX);

  Serial.print("\n\n");

  Serial.print("Displaying all regs\n");
  uint8_t memCounter = 0x80;
  uint8_t tempReadData;
  for(int rowi = 8; rowi < 16; rowi++ )
  {
    Serial.print("0x");
    Serial.print(rowi, HEX);
    Serial.print("0:");
    for(int coli = 0; coli < 16; coli++ )
    {
      tempReadData = mySensor.readRegister(memCounter);
      Serial.print((tempReadData >> 4) & 0x0F, HEX);//Print first hex nibble
      Serial.print(tempReadData & 0x0F, HEX);//Print second hex nibble
      Serial.print(" ");
      memCounter++;
    }
    Serial.print("\n");
  }
  
  
  Serial.print("\n\n");
  
  Serial.print("Displaying concatenated calibration words\n");
  Serial.print("dig_T1, uint16: ");
  Serial.println(mySensor.calibration.dig_T1);
  Serial.print("dig_T2, int16: ");
  Serial.println(mySensor.calibration.dig_T2);
  Serial.print("dig_T3, int16: ");
  Serial.println(mySensor.calibration.dig_T3);
  
  Serial.print("dig_P1, uint16: ");
  Serial.println(mySensor.calibration.dig_P1);
  Serial.print("dig_P2, int16: ");
  Serial.println(mySensor.calibration.dig_P2);
  Serial.print("dig_P3, int16: ");
  Serial.println(mySensor.calibration.dig_P3);
  Serial.print("dig_P4, int16: ");
  Serial.println(mySensor.calibration.dig_P4);
  Serial.print("dig_P5, int16: ");
  Serial.println(mySensor.calibration.dig_P5);
  Serial.print("dig_P6, int16: ");
  Serial.println(mySensor.calibration.dig_P6);
  Serial.print("dig_P7, int16: ");
  Serial.println(mySensor.calibration.dig_P7);
  Serial.print("dig_P8, int16: ");
  Serial.println(mySensor.calibration.dig_P8);
  Serial.print("dig_P9, int16: ");
  Serial.println(mySensor.calibration.dig_P9);
  
  Serial.print("dig_H1, uint8: ");
  Serial.println(mySensor.calibration.dig_H1);
  Serial.print("dig_H2, int16: ");
  Serial.println(mySensor.calibration.dig_H2);
  Serial.print("dig_H3, uint8: ");
  Serial.println(mySensor.calibration.dig_H3);
  Serial.print("dig_H4, int16: ");
  Serial.println(mySensor.calibration.dig_H4);
  Serial.print("dig_H5, int16: ");
  Serial.println(mySensor.calibration.dig_H5);
  Serial.print("dig_H6, uint8: ");
  Serial.println(mySensor.calibration.dig_H6);
    
  Serial.println();
//////////////////////////////////////////////
 /////ADXL362 
//    xl.begin(10);                   // Setup SPI protocol, issue device soft reset
//  xl.beginMeasure();              // Switch ADXL362 to measure mode  
///////////////////////


//////SD  
  while (!Serial) {
    ; // wait for serial port to connect. Needed for native USB port only
  }


  Serial.print("Initializing SD card...");

  // see if the card is present and can be initialized:
  if (!SD.begin(chipSelect)) {
    Serial.println("Card failed, or not present");
    // don't do anything more:
    return;
  }
  Serial.println("card initialized.");
////////////////////////////  
}

void loop() {
  
  int ntc;                
  double temp;            

  // make a string for assembling the data to log:
  String dataString = "";
  String dataString1 = "ahora ds18b20, ntc, sht15, bme280, sht15, bme280";
  

  // read three sensors and append to the string:
//  xl.readXYZTData(XValue, YValue, ZValue, Temperature);  //ADXL362
   
  tempC = sht15.readTemperatureC();  ///SHT15
  humidity = sht15.readHumidity();  ///SHT15

  ntc=analogRead(0);      //NTC
  temp=Thermistor(ntc);   //NTC

  float temp_BE=mySensor.readTempC();
  float hum_BE=mySensor.readFloatHumidity();
  float press_BE=mySensor.readFloatPressure();
  float alt_BE=mySensor.readFloatAltitudeMeters();
         
  float temp_ds = getTemp(); //ds18b20
    Serial.print("DS18B20: ");
    Serial.print(temp_ds);
//    Serial.print("  ADXL362: ");
//    Serial.print(Temperature-273); //adxl362
    Serial.print("  NTC: ");
    Serial.print(temp); //ntc
    Serial.print("  SHT15: ");
    Serial.print(tempC);//SHT15
    Serial.print("  BME280: ");
    Serial.println(temp_BE, 2);//BME280

    Serial.print("  SHT15: ");
    Serial.print(humidity);//SHT15
    Serial.print("%RH: ");
    Serial.println(hum_BE, 2);

    Serial.print("Pressure: ");
    Serial.print(press_BE, 2);
    Serial.print(" Pa");

    Serial.print("Altitude: ");
    Serial.print(alt_BE);
    Serial.println("m");

    
    dataString += String(temp_ds) + String (" ,") + String (temp)+ String (" ,") + String (tempC)+ String (" ,") + String (temp_BE)+ String (" ,") + String (humidity)+ String (" ,") + String (hum_BE)+ String (" ,") + String (press_BE)+ String (" ,") + String (alt_BE);
  
  // open the file. note that only one file can be open at a time,
  // so you have to close this one before opening another.
  File dataFile = SD.open("datalog.txt", FILE_WRITE);

  // if the file is available, write to it:
  if (dataFile) {
    if (x==0) {dataFile.println(dataString1); x=1;};
    dataFile.println(dataString);
    dataFile.close();
    // print to the serial port too:
    Serial.println(dataString);
    // delay(3000); 
  }
 
  // if the file isn't open, pop up an error:
  else {
    Serial.println("error opening datalog.txt");
  }
}

float getTemp(){
  //returns the temperature from one DS18S20 in DEG Celsius

  byte data[12];
  byte addr[8];

  if ( !ds.search(addr)) {
      //no more sensors on chain, reset search
      ds.reset_search();
      return -1000;
  }

  if ( OneWire::crc8( addr, 7) != addr[7]) {
      Serial.println("CRC is not valid!");
      return -1000;
  }

  if ( addr[0] != 0x10 && addr[0] != 0x28) {
      Serial.print("Device is not recognized");
      return -1000;
  }

  ds.reset();
  ds.select(addr);
  ds.write(0x44,1); // start conversion, with parasite power on at the end
  
  delay(750); // Wait for temperature conversion to complete

  byte present = ds.reset();
  ds.select(addr);    
  ds.write(0xBE); // Read Scratchpad

  
  for (int i = 0; i < 9; i++) { // we need 9 bytes
    data[i] = ds.read();
  }
  
  ds.reset_search();
  
  byte MSB = data[1];
  byte LSB = data[0];

  float tempRead = ((MSB << 8) | LSB); //using two's compliment
  float TemperatureSum = tempRead / 16;
  
  return TemperatureSum;
  
}
